elinucknack/led-strip-controller/led-strip-controller.kicad_sch

## KiCad design led-strip-controller.kicad_sch (2025-01-19)

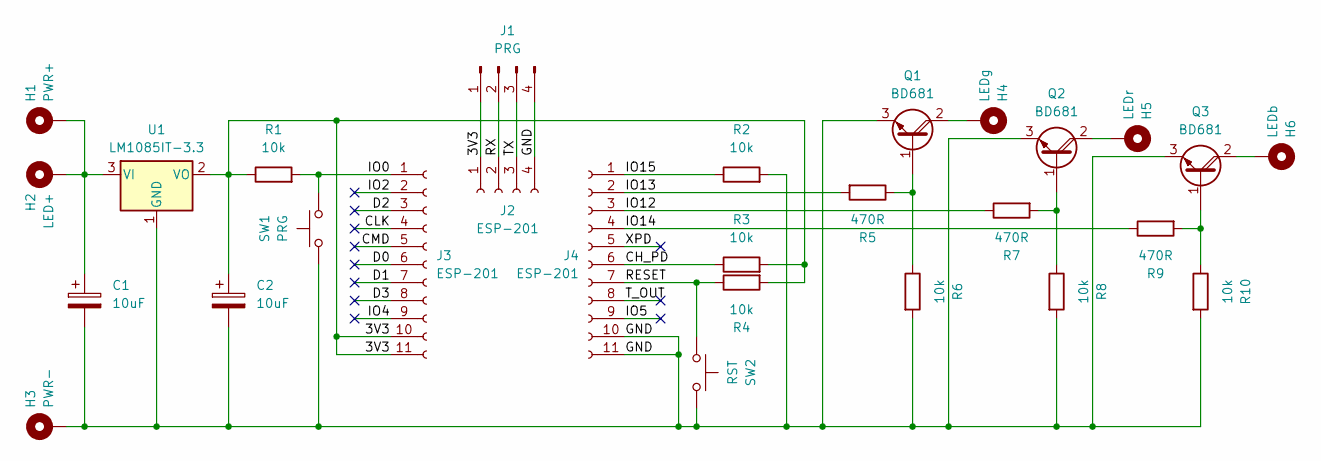
[picture p11: schematic led-strip-controller.kicad_sch]

Parts:
C1, C2: 10uF
H1: PWR+
H2: LED+
H3: PWR-
H4: LEDg
H5: LEDr
H6: LEDb
J1: PRG
J2, J3, J4: ESP-201
Q1, Q2, Q3: BD681
R1, R2, R3, R4, R6, R8, R10: 10k
R5, R7, R9: 470R
SW1: PRG
SW2: RST
U1: LM1085IT-3.3

Connections:
3V3: C2.1, J1.1, J2.1, J3.10, J3.11, R1.1, R3.2, R4.2, U1.2 (VO)
CH_PD: J4.6, R3.1
CLK: J3.4
CMD: J3.5
D0: J3.6
D1: J3.7
D2: J3.3
D3: J3.8
GND: C1.2, C2.2, H3.1, J1.4, J2.4, J4.10, J4.11, Q1.3 (E), Q2.3 (E), Q3.3 (E), R2.2, R6.2, R8.2, R10.2, SW1.2, SW2.2, U1.1 (GND)
IO0: J3.1, R1.2, SW1.1
IO2: J3.2
IO4: J3.9
IO5: J4.9
IO12: J4.3, R7.1
IO13: J4.2, R5.2
IO14: J4.4, R9.1
IO15: J4.1, R2.1
unnamed: C1.1, H1.1, H2.1, U1.3 (VI)
unnamed: H4.1, Q1.2 (C)
unnamed: H5.1, Q2.2 (C)
unnamed: H6.1, Q3.2 (C)
unnamed: Q1.1 (B), R5.1, R6.1
unnamed: Q2.1 (B), R7.2, R8.1
unnamed: Q3.1 (B), R9.2, R10.1
RESET: J4.7, R4.1, SW2.1
RX: J1.2, J2.2
TX: J1.3, J2.3
T_OUT: J4.8
XPD: J4.5
